mwuerms/round_timer/freecad/parts/rotary_encoder_PEC11R-4215K-S0024.step

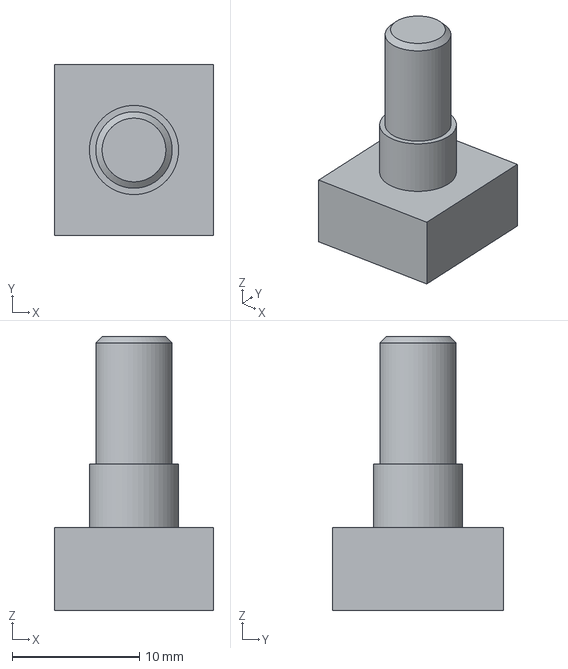
[picture p13: CAD file, 2025-02-10]
freecad/parts/rotary_encoder_PEC11R-4215K-S0024.step
12.5 x 13.4 x 21.5 mm
