mwuerms/round_timer/freecad/parts/PER601-P117-N0015.stp

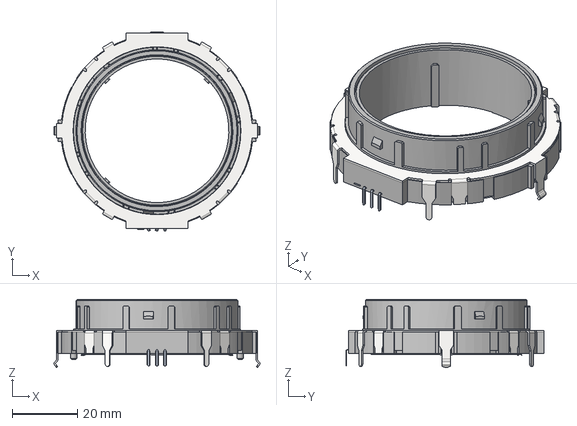
[picture p14: CAD file, 2025-02-10]
freecad/parts/PER601-P117-N0015.stp
63.1 x 61.1 x 20.8 mm
