mwuerms/round_timer/freecad/parts/speaker_CMS-3047-18L300-speaker.step

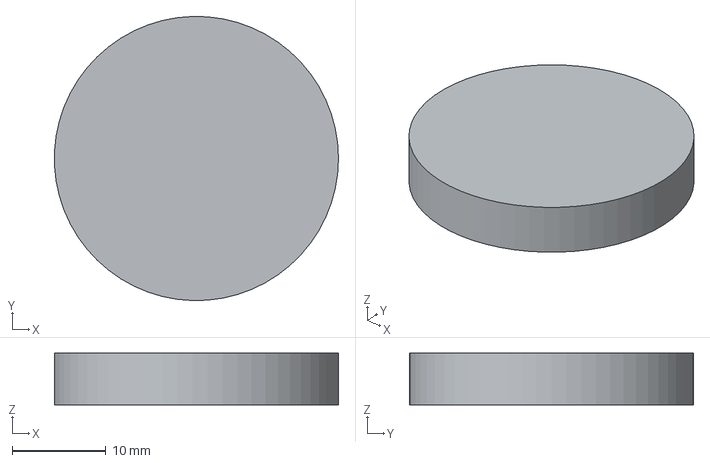
[picture p15: CAD file, 2025-02-10]
freecad/parts/speaker_CMS-3047-18L300-speaker.step
30.3 x 30.3 x 5.50 mm
