mwuerms/round_timer/freecad/parts/dfplayer_pcb-player.step

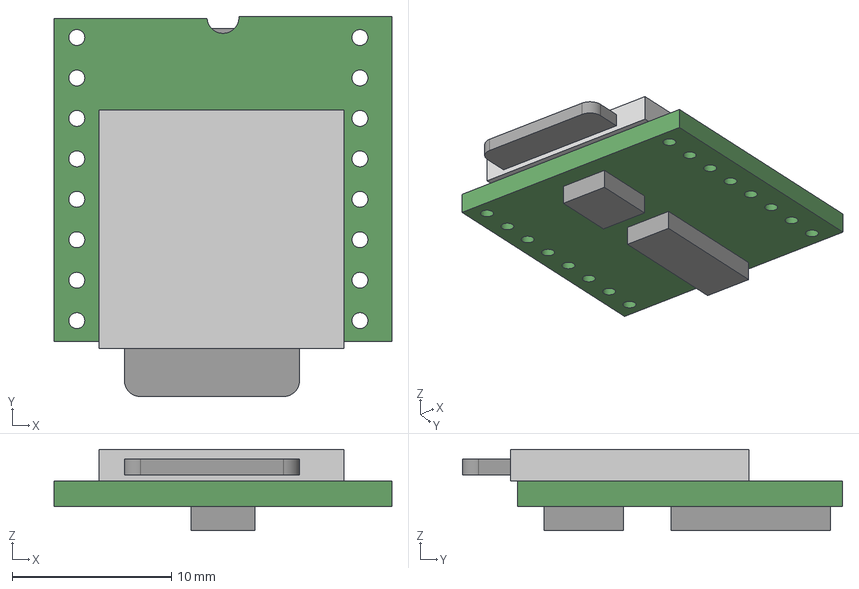
[picture p16: CAD file, 2025-02-10]
freecad/parts/dfplayer_pcb-player.step
21.2 x 23.9 x 5.10 mm
PCB
usdcard holder
usdcard
SOIC-16
SOIC-8
