mwuerms/round_timer/freecad/parts/round_1.28_inch_display_cut.step

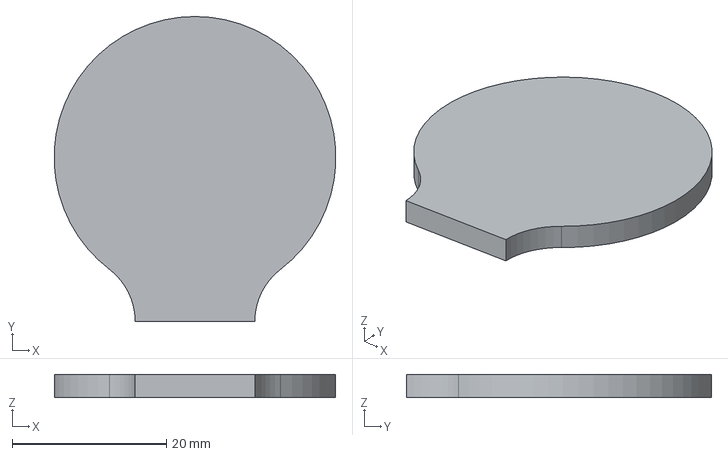
[picture p17: CAD file, 2025-02-10]
freecad/parts/round_1.28_inch_display_cut.step
36.5 x 39.5 x 3.00 mm
