mwuerms/round_timer/freecad/parts/round_1.28_inch_display.step

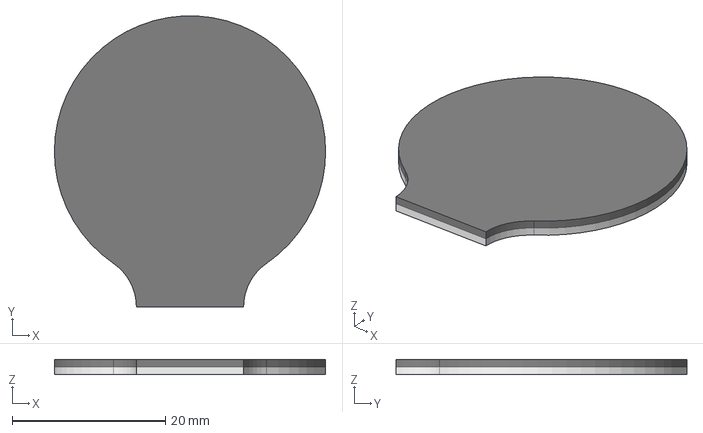
[picture p18: CAD file, 2025-02-10]
freecad/parts/round_1.28_inch_display.step
35.4 x 38.0 x 2.00 mm
black glass
pcb
