mwuerms/round_timer/stm32/disp1/Core/Src/fifo.c

/**
 * Martin Egli
 * 2023-09-02
 * mmlib https://github.com/mwuerms/mmlib
 * fifo functions
 */

#include "fifo.h"

// - public functions ----------------------------------------------------------
uint16_t fifo_init(fifo_t *f, void *data, uint16_t size) {
    if(f == NULL) {
        // error, invalid pointer
        return false;
    }
    f->data = data;
    f->size = size;
    f->wr = 0;
    f->wr_proc = 0;
    f->rd = 0;
    f->rd_proc = 0;
    return true;
}

static inline uint16_t fifo_is_full_inline(fifo_t *f) {
    uint16_t wr_next;
    wr_next = fifo_next_pos(f->wr, f->size);
    if(wr_next == f->rd) {
        // is full
        return true;
    }
    return false;
}

uint16_t fifo_is_full(fifo_t *f) {
    if(f == NULL) {
        // error, invalid pointer
        return false;
    }
    return fifo_is_full_inline(f);
}

static inline uint16_t fifo_is_empty_inline(fifo_t *f) {
    if(f->rd == f->wr) {
        // is empty
        return true;
    }
    return false;
}

uint16_t fifo_is_empty(fifo_t *f) {
    uint16_t rd_next;
    if(f == NULL) {
        // error, invalid pointer
        return false;
    }
    return fifo_is_empty_inline(f);
}

uint16_t fifo_try_append(fifo_t *f) {
    if(f == NULL) {
        // error, invalid pointer
        return false;
    }
    if(fifo_is_full_inline(f) == true) {
        // error, is full
        return false;
    }
    f->wr_proc = fifo_next_pos(f->wr, f->size);
    return true;
}

uint16_t fifo_finalize_append(fifo_t *f) {
    if(f == NULL) {
        // error, invalid pointer
        return false;
    }
    f->wr = f->wr_proc;
    return true;
}

uint16_t fifo_try_get(fifo_t *f) {
    if(f == NULL) {
        // error, invalid pointer
        return false;
    }
    if(fifo_is_empty(f) == true) {
        // error, is empty
        return false;
    }
    f->rd_proc = fifo_next_pos(f->rd, f->size);
    return true;
}

uint16_t fifo_finalize_get(fifo_t *f) {
    if(f == NULL) {
        // error, invalid pointer
        return false;
    }
    f->rd = f->rd_proc;
    return true;
}

uint16_t fifo_next_pos(uint16_t pos, uint16_t size) {
    pos++;
    if(pos >= size)
        return 0;
    return pos;
}

uint16_t fifo_prev_pos(uint16_t pos, uint16_t size) {
    if(pos == 0)
        return size-1;
    return pos-1;
}
