mwuerms/round_timer/stm32/disp1/Core/Src/usr_in.c

/**
 * module usr_in "User Inputs"
 * Martin, 2025-02-26
 */

#include "usr_in.h"
#include "stdbool.h"
#include "scheduler.h"
#include "app.h"
#include "lptim.h"

// - events, see app (receiver)

// - GPIOs ------------------------------------
#include "main.h"
// BTN0_GPIO_Port, BTN0_Pin
// BTN1_GPIO_Port, BTN1_Pin
// BTN2_GPIO_Port, BTN2_Pin
// ENC_A_GPIO_Port, ENC_A_Pin
// ENC_B_GPIO_Port, ENC_B_Pin
#define IS_BTN0_LOW() ((BTN0_GPIO_Port->IDR & BTN0_Pin) == 0)
#define IS_BTN1_LOW() ((BTN1_GPIO_Port->IDR & BTN1_Pin) == 0)
#define IS_BTN2_LOW() ((BTN2_GPIO_Port->IDR & BTN2_Pin) == 0)
#define IS_ENC_A_LOW() ((ENC_A_GPIO_Port->IDR & ENC_A_Pin) == 0)
#define IS_ENC_B_LOW() ((ENC_B_GPIO_Port->IDR & ENC_B_Pin) == 0)

// count encoder steps, --: left, ++: right
static volatile int16_t enc_abs_count = 0; // absolute, cannot be reseted
static volatile int16_t enc_rel_count = 0; // relative, reset after reading

void HAL_GPIO_EXTI_Callback(uint16_t GPIO_Pin) {
	// BTN0_Pin
	if(GPIO_Pin == BTN0_Pin) {
		if(IS_BTN0_LOW()) {
			// pressed
			scheduler_send_event(app_ev_task_id, EV_BTN0_PRESSED, NULL);
		}
		else {
			// released
			scheduler_send_event(app_ev_task_id, EV_BTN0_RELEASED, NULL);
		}
	}
	// BTN1_Pin
	if(GPIO_Pin == BTN1_Pin) {
		if(IS_BTN1_LOW()) {
			// pressed
			scheduler_send_event(app_ev_task_id, EV_BTN1_PRESSED, NULL);
		}
		else {
			// released
			scheduler_send_event(app_ev_task_id, EV_BTN1_RELEASED, NULL);
		}
	}
	// BTN2_Pin
	if(GPIO_Pin == BTN2_Pin) {
		if(IS_BTN2_LOW()) {
			// pressed
			scheduler_send_event(app_ev_task_id, EV_BTN2_PRESSED, NULL);
		}
		else {
			// released
			scheduler_send_event(app_ev_task_id, EV_BTN2_RELEASED, NULL);
		}
	}
	// ENC_A_Pin + ENC_B_Pin
	if(GPIO_Pin == ENC_A_Pin) {
		if(IS_ENC_A_LOW()) {
			if(IS_ENC_B_LOW()) {
				// left
				scheduler_send_event(app_ev_task_id, EV_ENC_LEFT, NULL);
				enc_abs_count--;
				enc_rel_count--;
			}
			else {
				// right
				scheduler_send_event(app_ev_task_id, EV_ENC_RIGHT, NULL);
				enc_abs_count++;
				enc_rel_count++;
			}
		}
		else {
			if(IS_ENC_B_LOW()) {
				// right
				scheduler_send_event(app_ev_task_id, EV_ENC_RIGHT, NULL);
				enc_abs_count++;
				enc_rel_count++;
			}
			else {
				// left
				scheduler_send_event(app_ev_task_id, EV_ENC_LEFT, NULL);
				enc_abs_count--;
				enc_rel_count--;
			}
		}
	}
}

void usr_in_init(void) {
	return;
}

void usr_in_enable(uint32_t mask) {
	return;
}

void usr_in_disable(uint32_t mask) {
	return;
}

int16_t usr_in_get_enc_abs_count(void) {
	return enc_abs_count;
}

int16_t usr_in_get_enc_rel_count(void) {
	return enc_rel_count;
}
