mwuerms/round_timer/stm32/rtimer02/Core/Inc/usr_in.h

/**
 * module usr_in "User Inputs"
 * Martin, 2025-02-26
 */

#ifndef _USR_IN_H_
#define _USR_IN_H_

#ifdef __cplusplus
extern "C" {
#endif

#include "stdint.h"

// - timeout isr --------------
void usr_in_timout_isr(void);

// - public functions ---------
void usr_in_init(void);

#define USR_IN_BTN0_MASK (1 << 0)
#define USR_IN_BTN1_MASK (1 << 1)
#define USR_IN_BTN2_MASK (1 << 2)
#define USR_IN_ENC_MASK (1 << 3)
void usr_in_enable(uint32_t mask);
void usr_in_disable(uint32_t mask);

int16_t usr_in_get_enc_abs_count(void);
int16_t usr_in_get_enc_rel_count(void);

#ifdef __cplusplus
}
#endif

#endif // _USR_IN_H_
