mwuerms/round_timer/stm32/disp1/Core/Inc/timer_app.h

/**
 * timer_app, timer application
 * Martin, 2025-02-26
 */

#ifndef _TIMER_APP_H_
#define _TIMER_APP_H_

#ifdef __cplusplus
extern "C" {
#endif

#include "stdint.h"

void timer_app_init(void);

#ifdef __cplusplus
}
#endif

#endif // _TIMER_APP_H_
